SeedSigner/seedsigner/docs/Seed_QR_Card.pdf

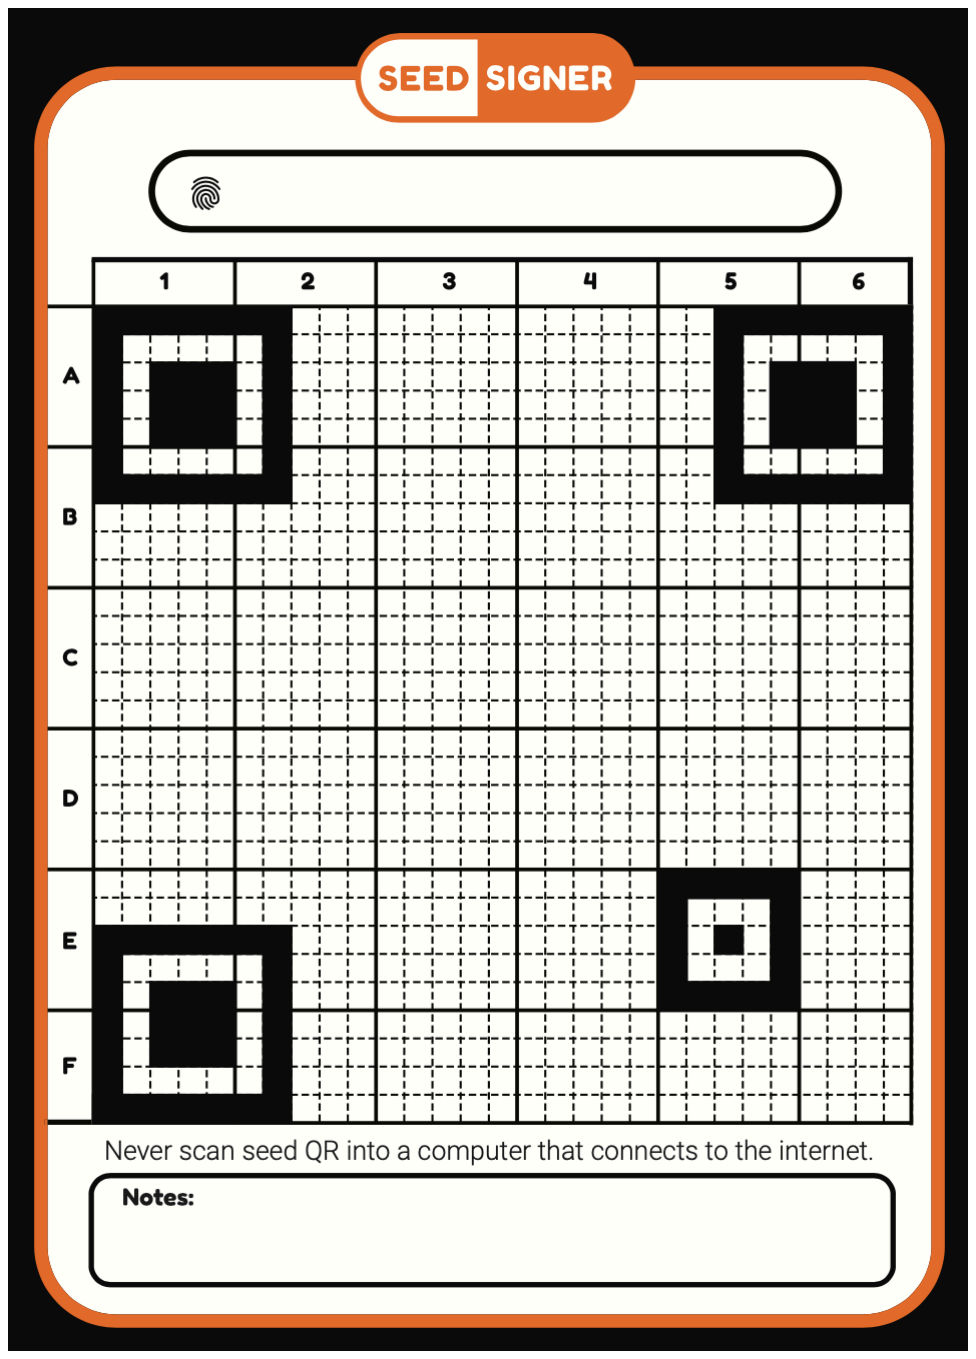
[picture p57: figure]
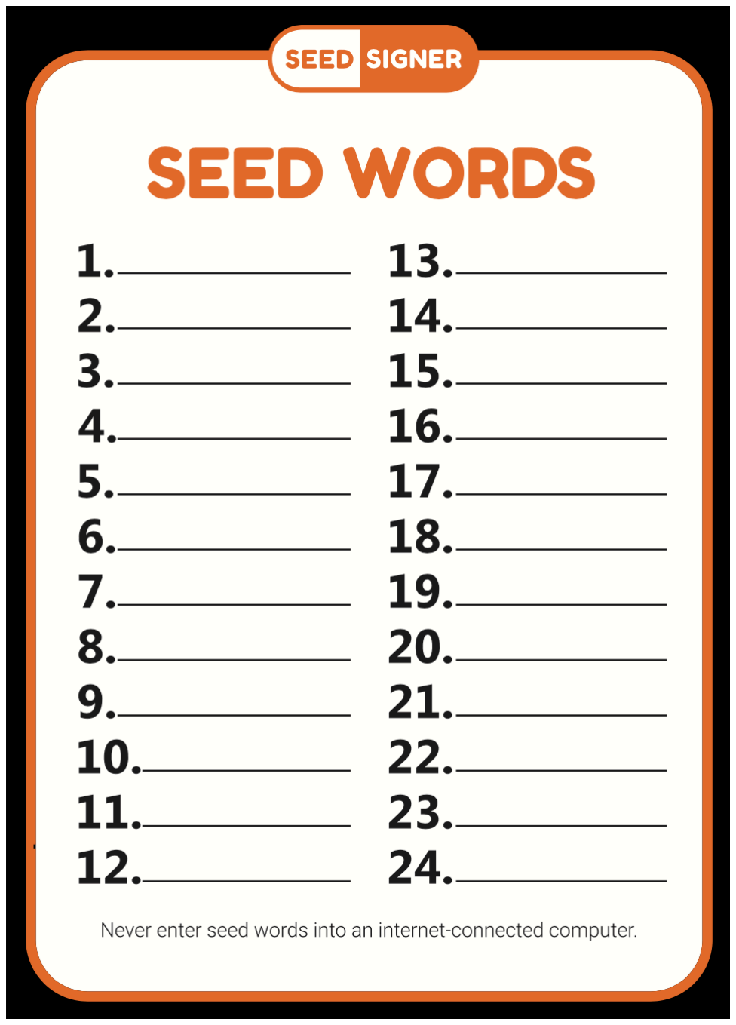
[picture p58: figure]
