SeedSigner/seedsigner/docs/img/dice_pic1.png

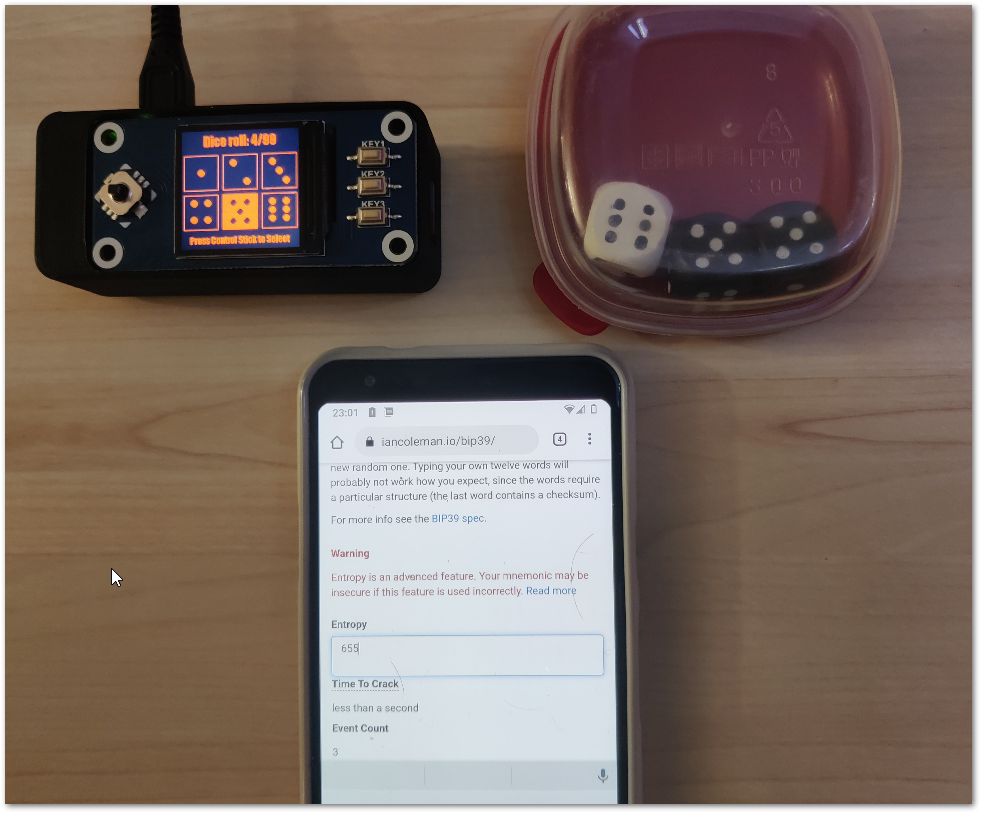
docs/img/dice_pic1.png
