SeedSigner/seedsigner/docs/img/dice_pic2.png

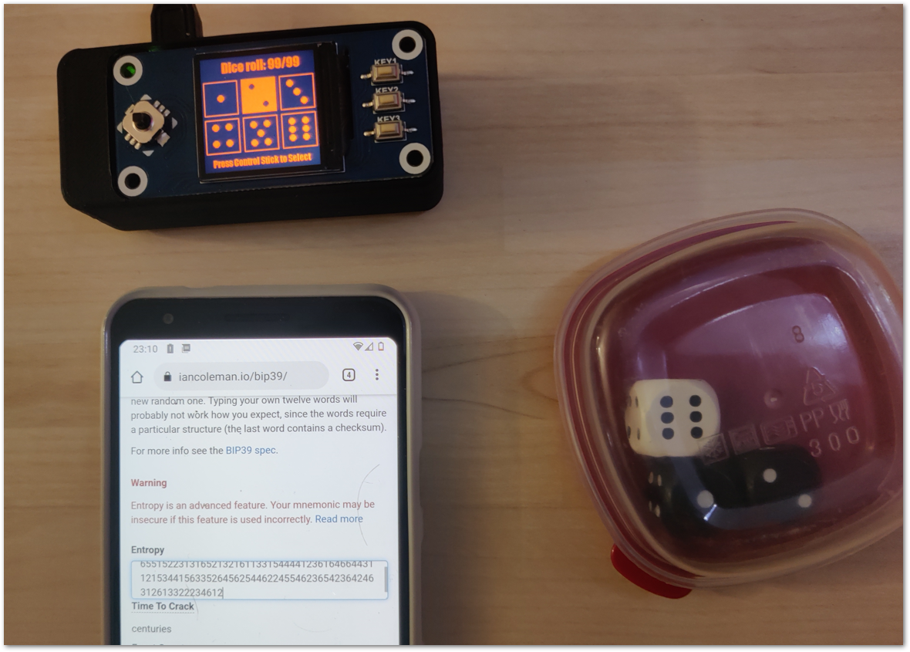
docs/img/dice_pic2.png
