SeedSigner/seedsigner/docs/img/dice_pic3.png

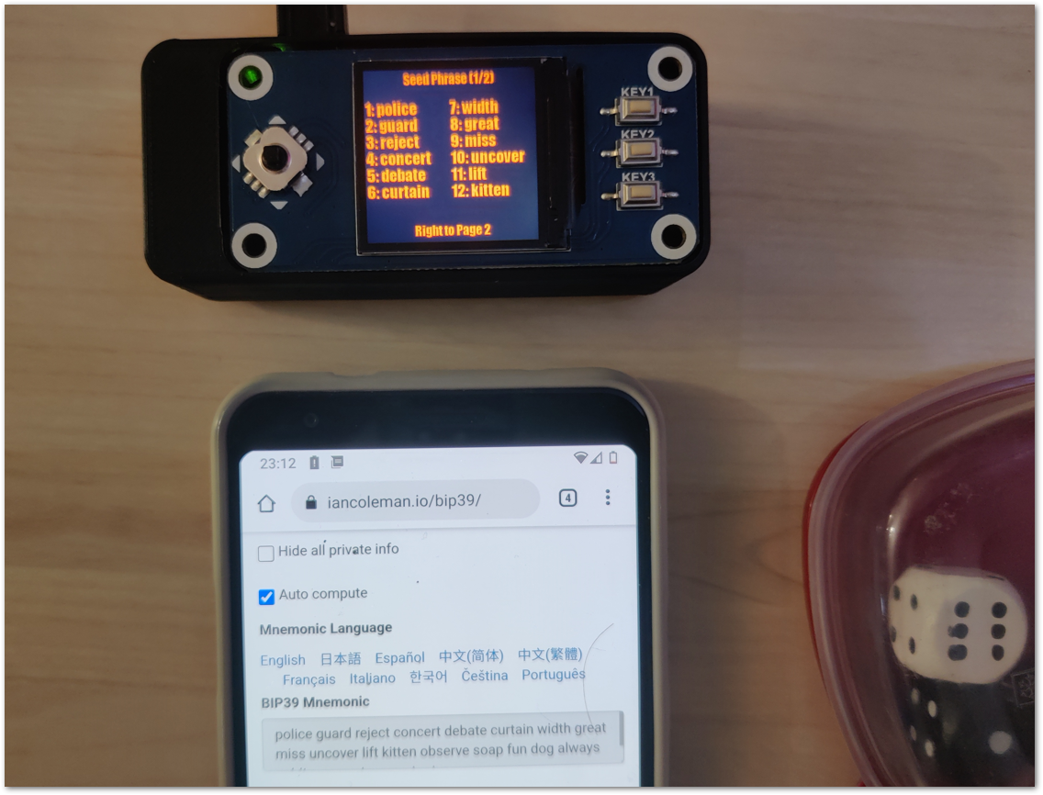
docs/img/dice_pic3.png
