SeedSigner/seedsigner/docs/img/dice_type.png

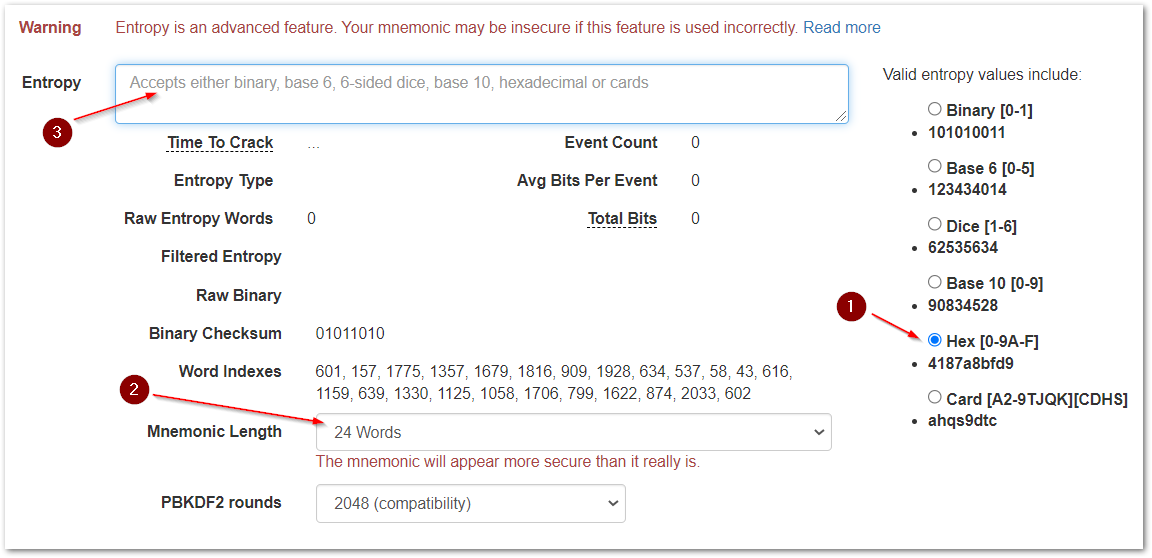
docs/img/dice_type.png
