SeedSigner/seedsigner/docs/img/Open_Pill_Star.JPG

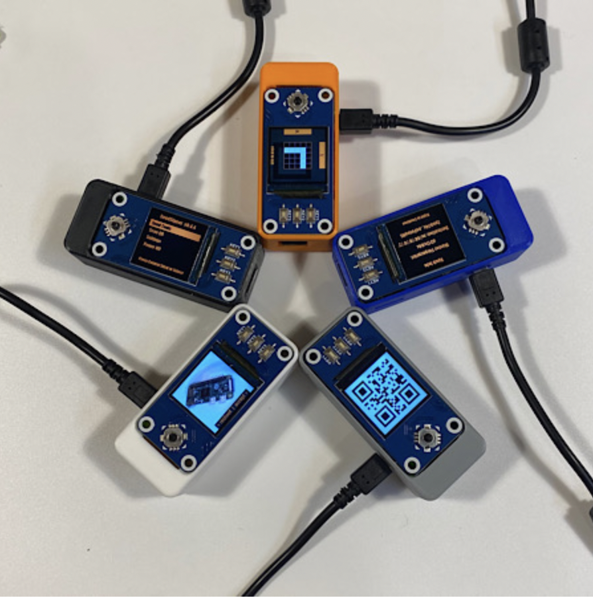
docs/img/Open_Pill_Star.JPG
