SeedSigner/seedsigner/docs/img/Orange_Pill.JPG

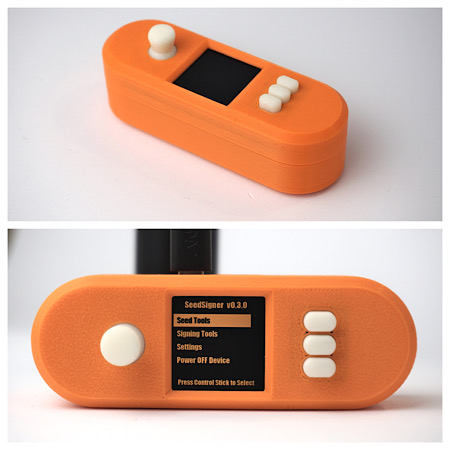
docs/img/Orange_Pill.JPG
