SeedSigner/seedsigner/docs/seed_qr/img/compact_12word.png

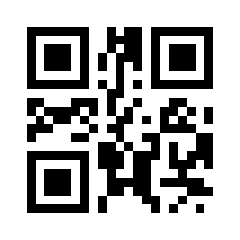
docs/seed_qr/img/compact_12word.png
