SeedSigner/seedsigner/docs/seed_qr/img/compact_24word.png

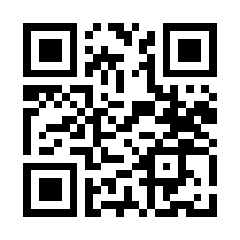
docs/seed_qr/img/compact_24word.png
