SeedSigner/seedsigner/docs/seed_qr/img/standard_24word.png

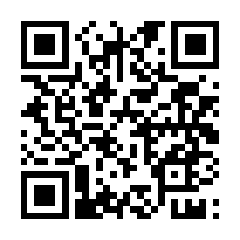
docs/seed_qr/img/standard_24word.png
