SeedSigner/seedsigner/enclosures/rugged_pill/Multimaterial/RuggedPill_Top_MMU.3mf

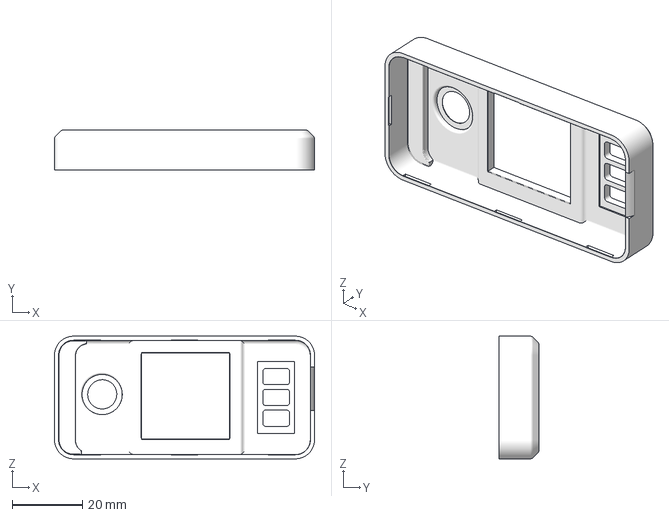
[picture p84: CAD file, 2023-07-31]
enclosures/rugged_pill/Multimaterial/RuggedPill_Top_MMU.3mf
73.8 x 11.3 x 34.8 mm
Circumference (4)
Top_MMU
