SeedSigner/seedsigner/enclosures/rugged_pill/RuggedPill_Thumbstick.stl

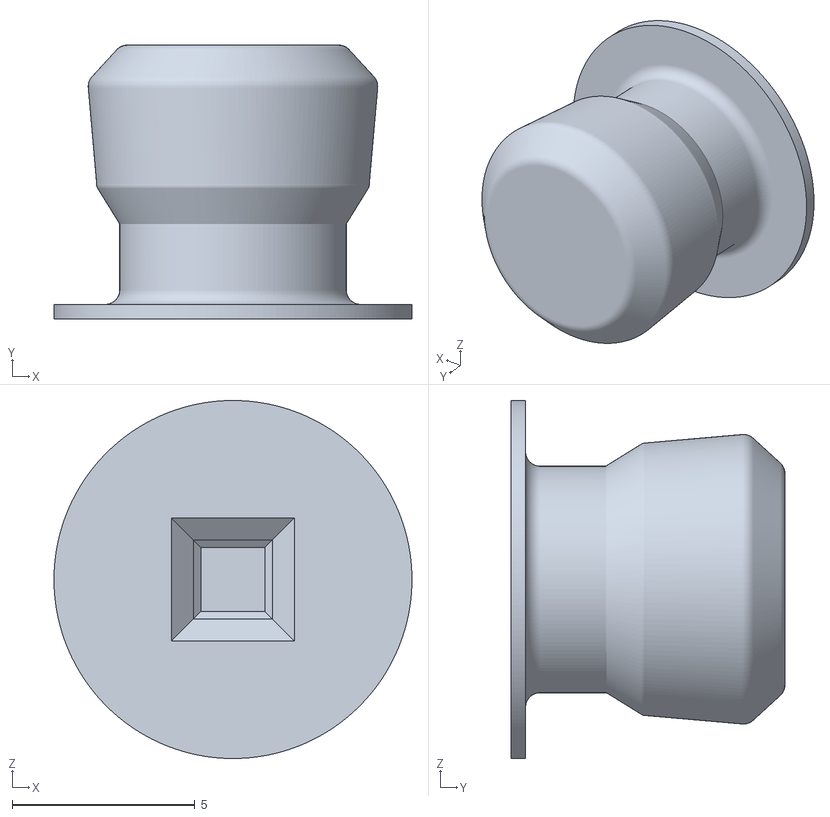
[picture p85: CAD file, 2023-07-31]
enclosures/rugged_pill/RuggedPill_Thumbstick.stl
9.80 x 7.50 x 9.80
