SeedSigner/seedsigner/enclosures/simple_pill/protective_case/sp_protective_case_upper.stl

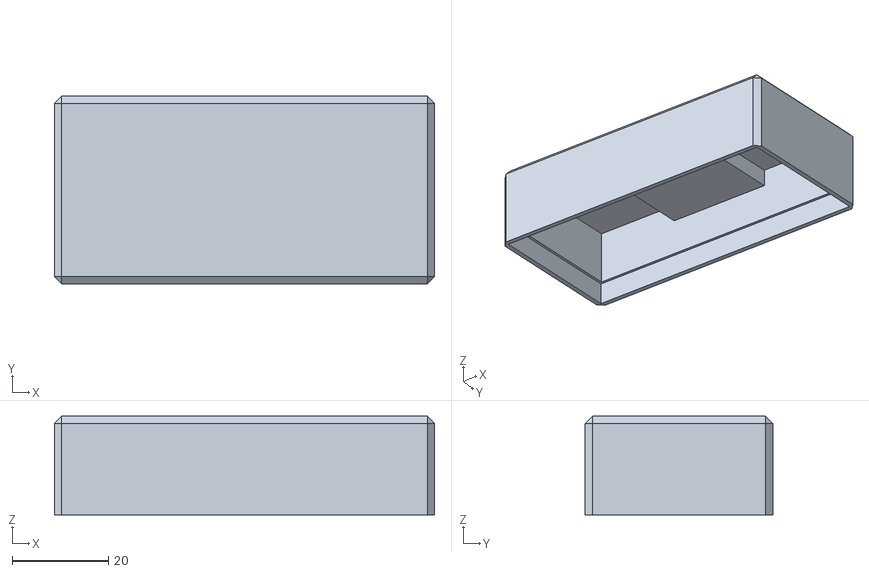
[picture p86: CAD file, 2022-12-02]
enclosures/simple_pill/protective_case/sp_protective_case_upper.stl
79.0 x 39.0 x 20.5
