SeedSigner/seedsigner/enclosures/simple_pill/sp_upper.stl

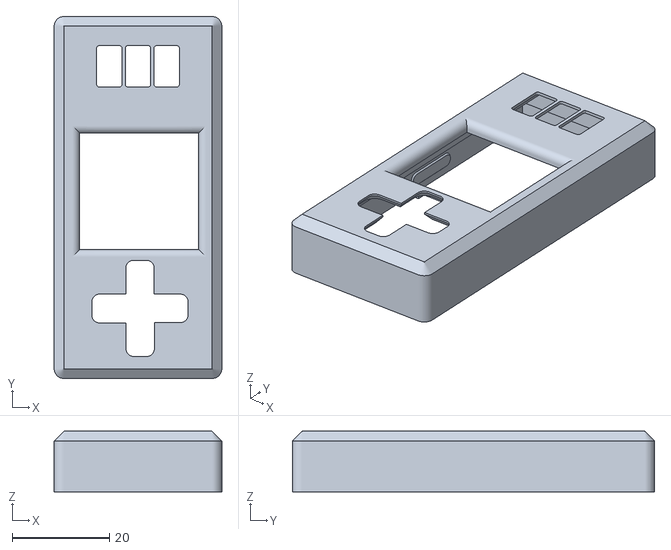
[picture p87: CAD file, 2022-05-04]
enclosures/simple_pill/sp_upper.stl
34.5 x 74.5 x 12.5
