SeedSigner/seedsigner/enclosures/open_pill_mini_w_coverplate/Thumbstick_TPU.stl

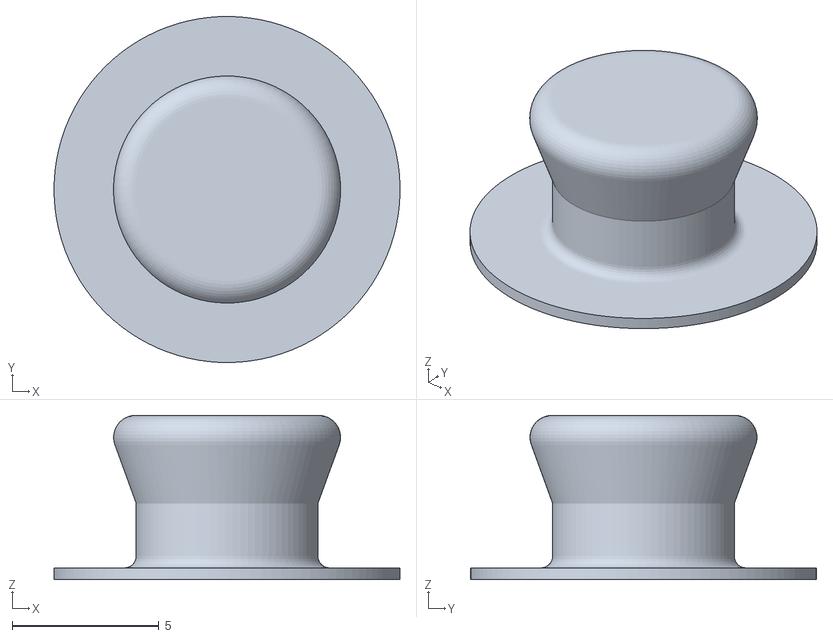
[picture p88: CAD file, 2023-02-14]
enclosures/open_pill_mini_w_coverplate/Thumbstick_TPU.stl
11.8 x 11.8 x 5.60
