SeedSigner/seedsigner/enclosures/orange_pill/print_files/button.stl

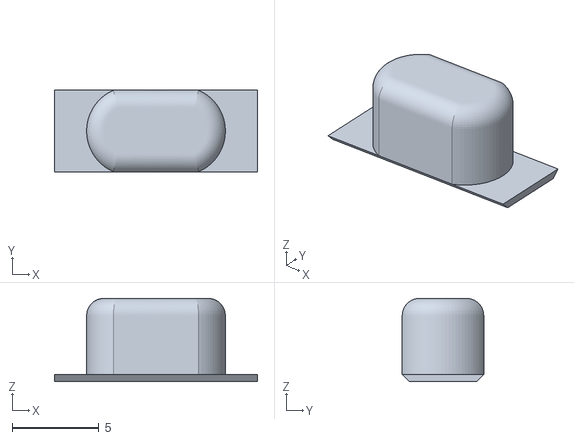
[picture p89: CAD file, 2021-04-17]
enclosures/orange_pill/print_files/button.stl
11.7 x 4.70 x 4.80
