SeedSigner/seedsigner/enclosures/pushcase/3mf/Top - Push Case - SeedSigner.3mf

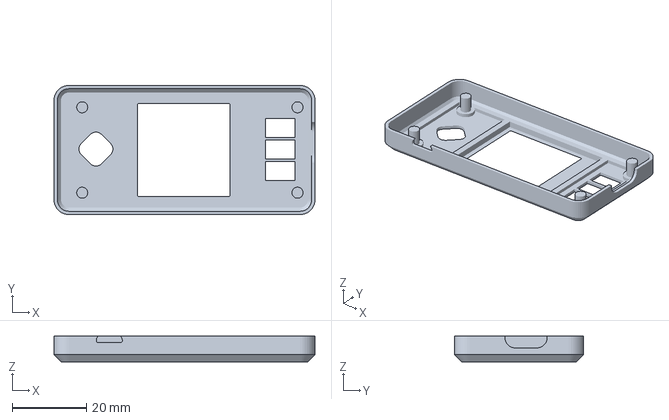
[picture p90: CAD file, 2024-07-11]
enclosures/pushcase/3mf/Top - Push Case - SeedSigner.3mf
70.3 x 34.8 x 7.00 mm
