SeedSigner/seedsigner/enclosures/rugged_pill/RuggedPill_Top.stl

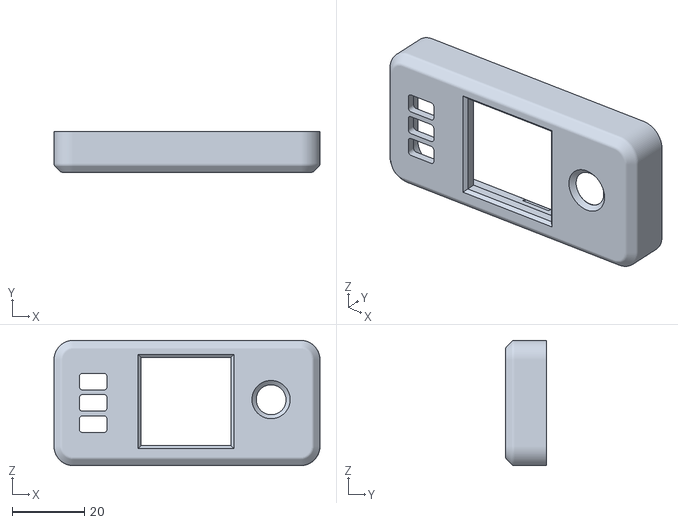
[picture p91: CAD file, 2023-07-31]
enclosures/rugged_pill/RuggedPill_Top.stl
73.8 x 11.3 x 34.8
