SeedSigner/seedsigner/enclosures/simple_pill/sp_button.stl

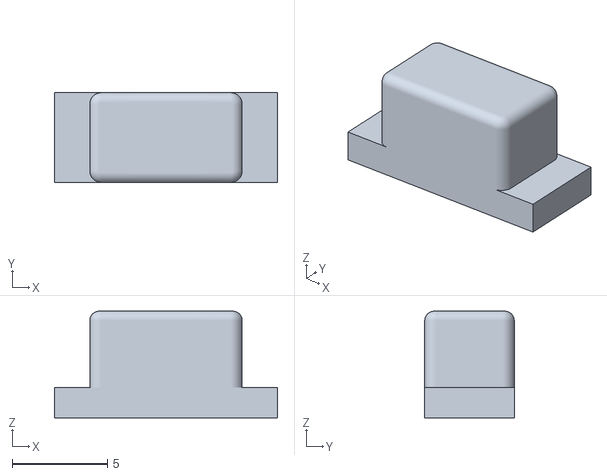
[picture p92: CAD file, 2022-05-04]
enclosures/simple_pill/sp_button.stl
11.7 x 4.70 x 5.60
