SeedSigner/seedsigner/enclosures/open_pill_mini_w_coverplate/Thumbstick_PLA.stl

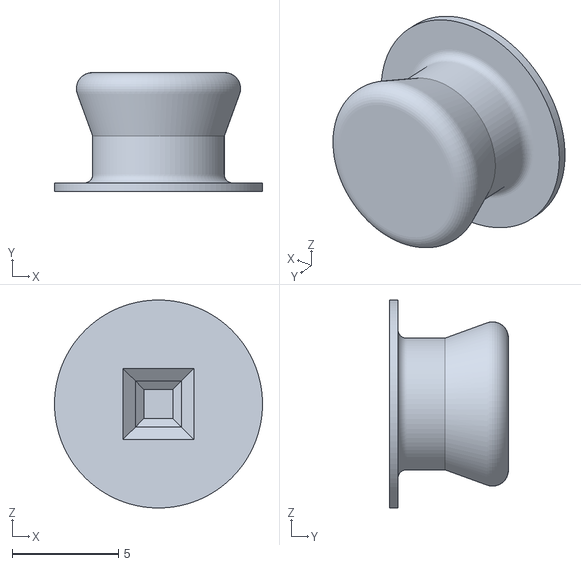
[picture p93: CAD file, 2023-02-14]
enclosures/open_pill_mini_w_coverplate/Thumbstick_PLA.stl
9.80 x 5.60 x 9.79
