SeedSigner/seedsigner/enclosures/orange_pill/print_files/OP_Upper.stl

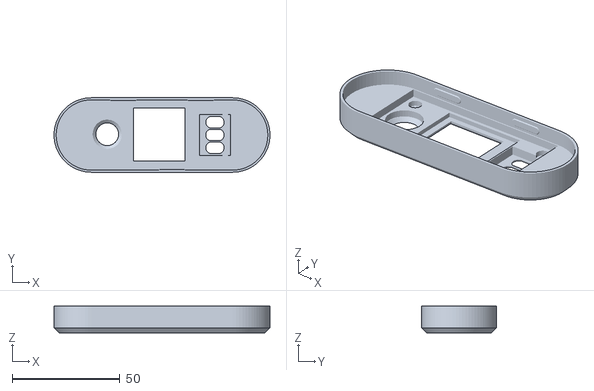
[picture p94: CAD file, 2021-04-17]
enclosures/orange_pill/print_files/OP_Upper.stl
100.0 x 34.5 x 12.5
