SeedSigner/seedsigner/enclosures/pushcase/3mf/Soldering Support - Push Case - SeedSigner.3mf

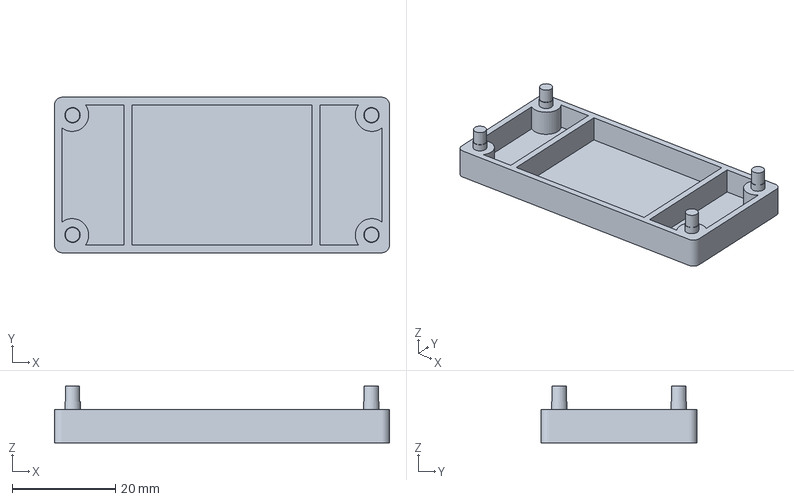
[picture p95: CAD file, 2024-07-11]
enclosures/pushcase/3mf/Soldering Support - Push Case - SeedSigner.3mf
65.0 x 30.2 x 11.0 mm
