SeedSigner/seedsigner/enclosures/rugged_pill/RuggedPill_Trackball.stl

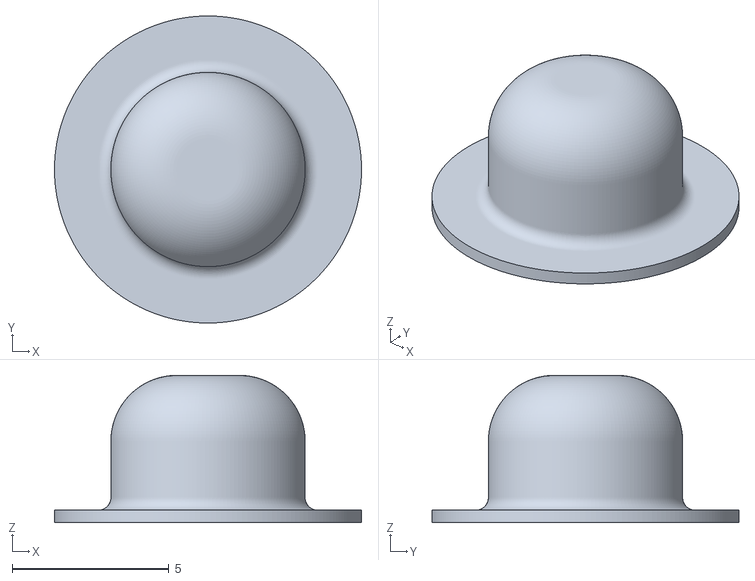
[picture p96: CAD file, 2023-07-31]
enclosures/rugged_pill/RuggedPill_Trackball.stl
9.80 x 9.80 x 4.70
