SeedSigner/seedsigner/enclosures/simple_pill/sp_dpad.stl

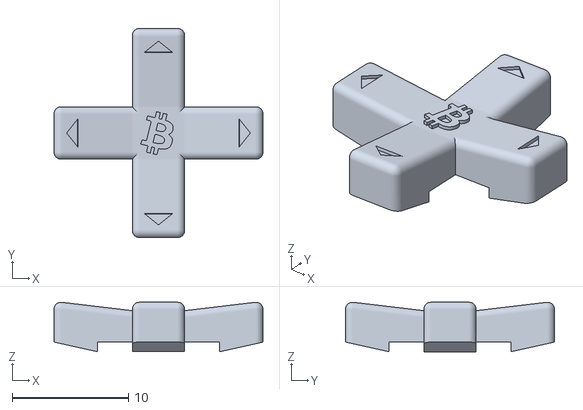
[picture p97: CAD file, 2022-05-04]
enclosures/simple_pill/sp_dpad.stl
18.0 x 18.0 x 4.26
