SeedSigner/seedsigner/enclosures/open_pill_mini_w_coverplate/Buttons.stl

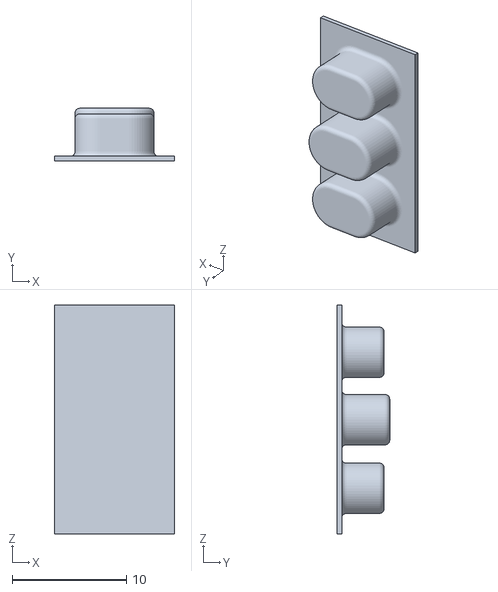
[picture p98: CAD file, 2023-02-14]
enclosures/open_pill_mini_w_coverplate/Buttons.stl
10.5 x 4.60 x 20.0
