SeedSigner/seedsigner/enclosures/pushcase/3mf/Middle - Push Case - SeedSigner.3mf

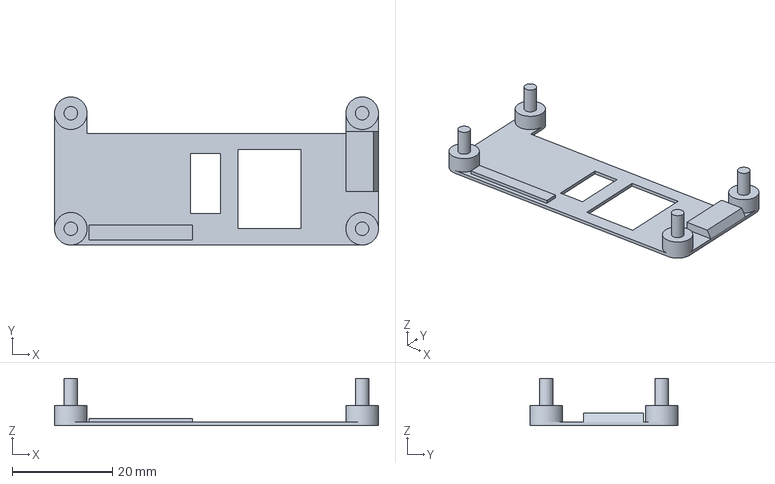
[picture p99: CAD file, 2024-07-11]
enclosures/pushcase/3mf/Middle - Push Case - SeedSigner.3mf
64.5 x 29.5 x 9.40 mm
