SeedSigner/seedsigner/enclosures/rugged_pill/RuggedPill_Buttons.stl

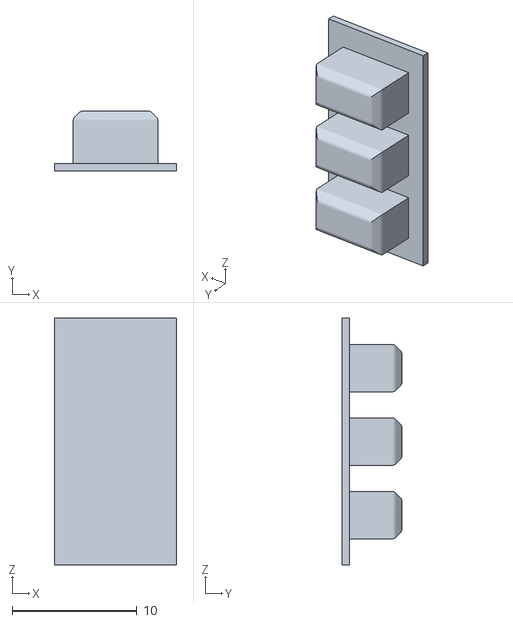
[picture p100: CAD file, 2023-07-31]
enclosures/rugged_pill/RuggedPill_Buttons.stl
9.80 x 4.80 x 19.8
