SeedSigner/seedsigner/docs/seed_qr/printable_templates/grid_wfingerprint_21x21_4-up.pdf

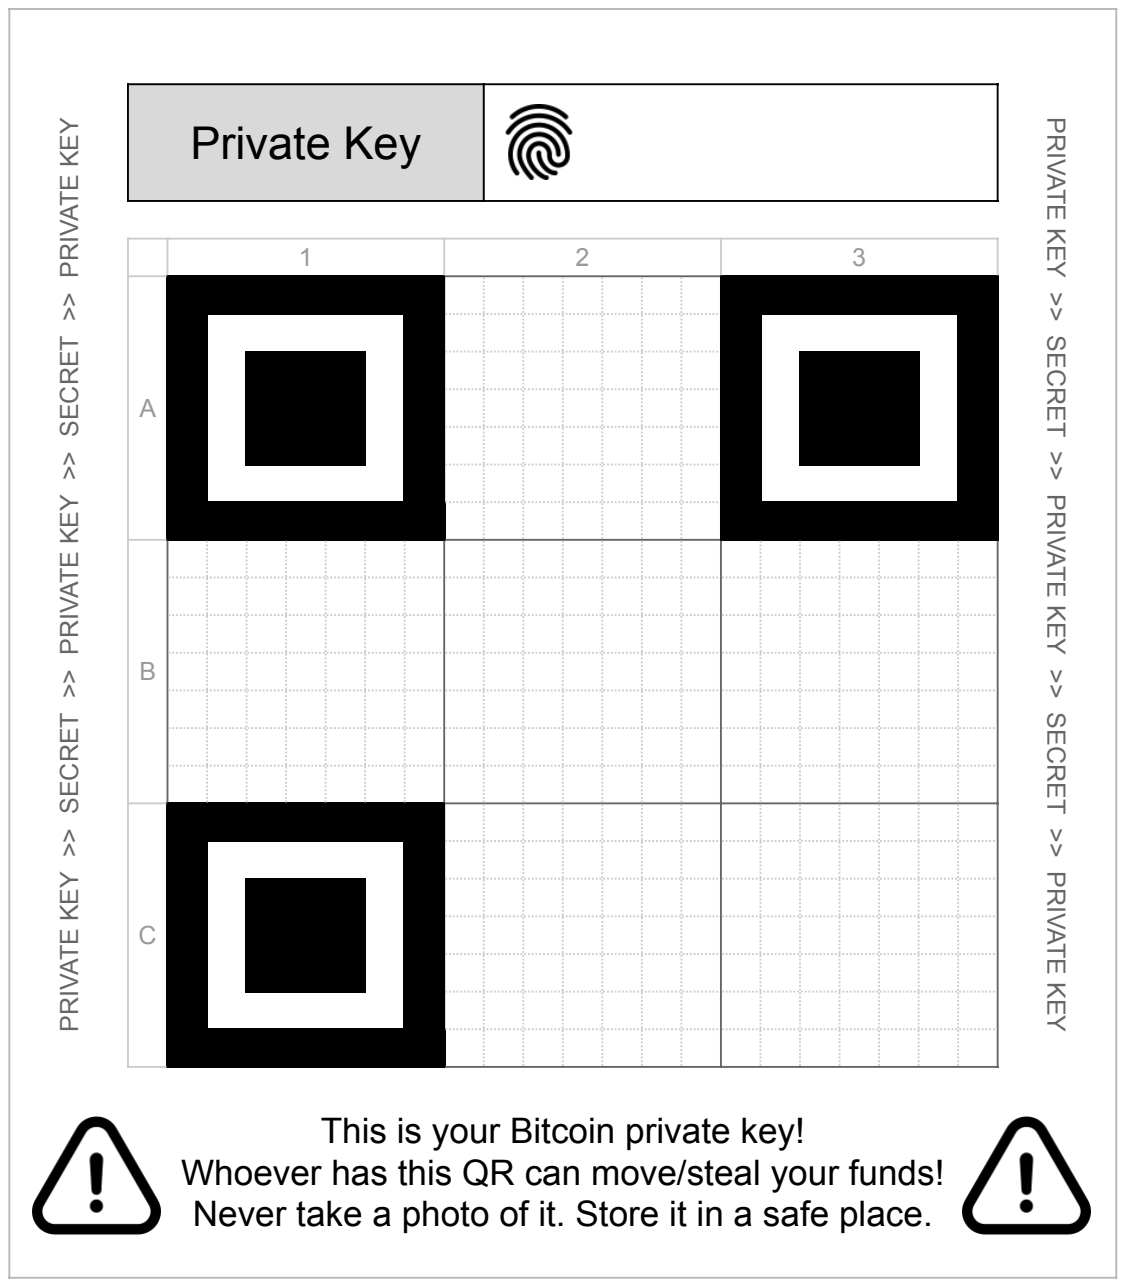
[picture p109: figure]
Private Key; This is your Bitcoin private key!

PRIVATE KEY >> SECRET >> PRIVATE KEY >> SECRET >> PRIVATE KEY PRIVATE KEY >> SECRET >> PRIVATE KEY >> SECRET >> PRIVATE KEY

Whoever has this QR can move/steal your funds! Never take a photo of it. Store it in a safe place.

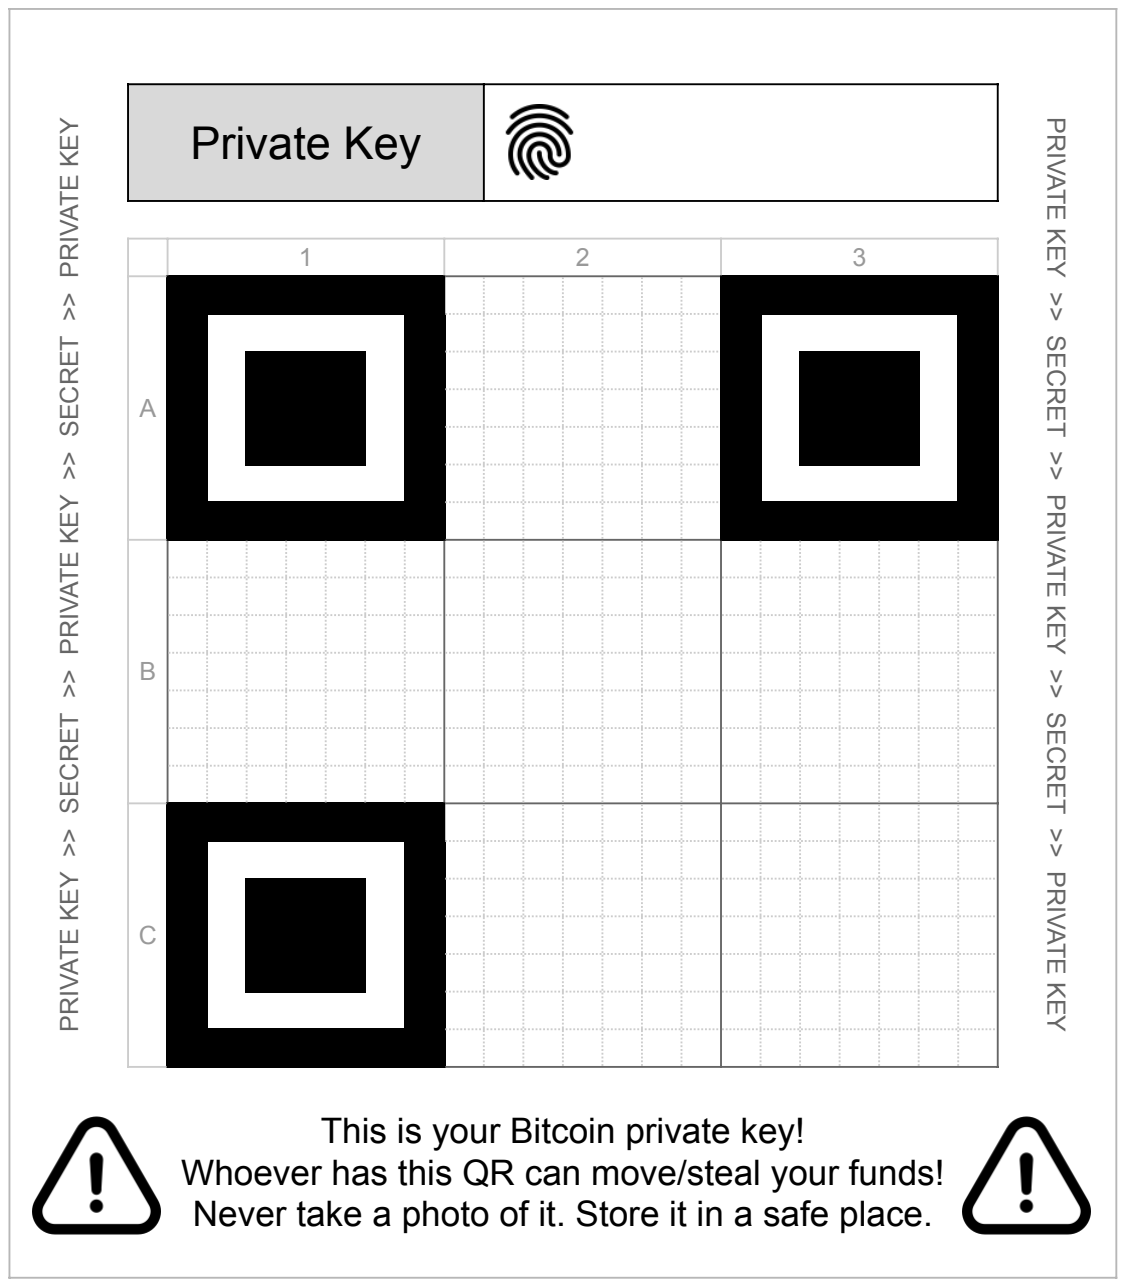
[picture p110: figure]
Private Key; This is your Bitcoin private key!

PRIVATE KEY >> SECRET >> PRIVATE KEY >> SECRET >> PRIVATE KEY PRIVATE KEY >> SECRET >> PRIVATE KEY >> SECRET >> PRIVATE KEY

Whoever has this QR can move/steal your funds! Never take a photo of it. Store it in a safe place.

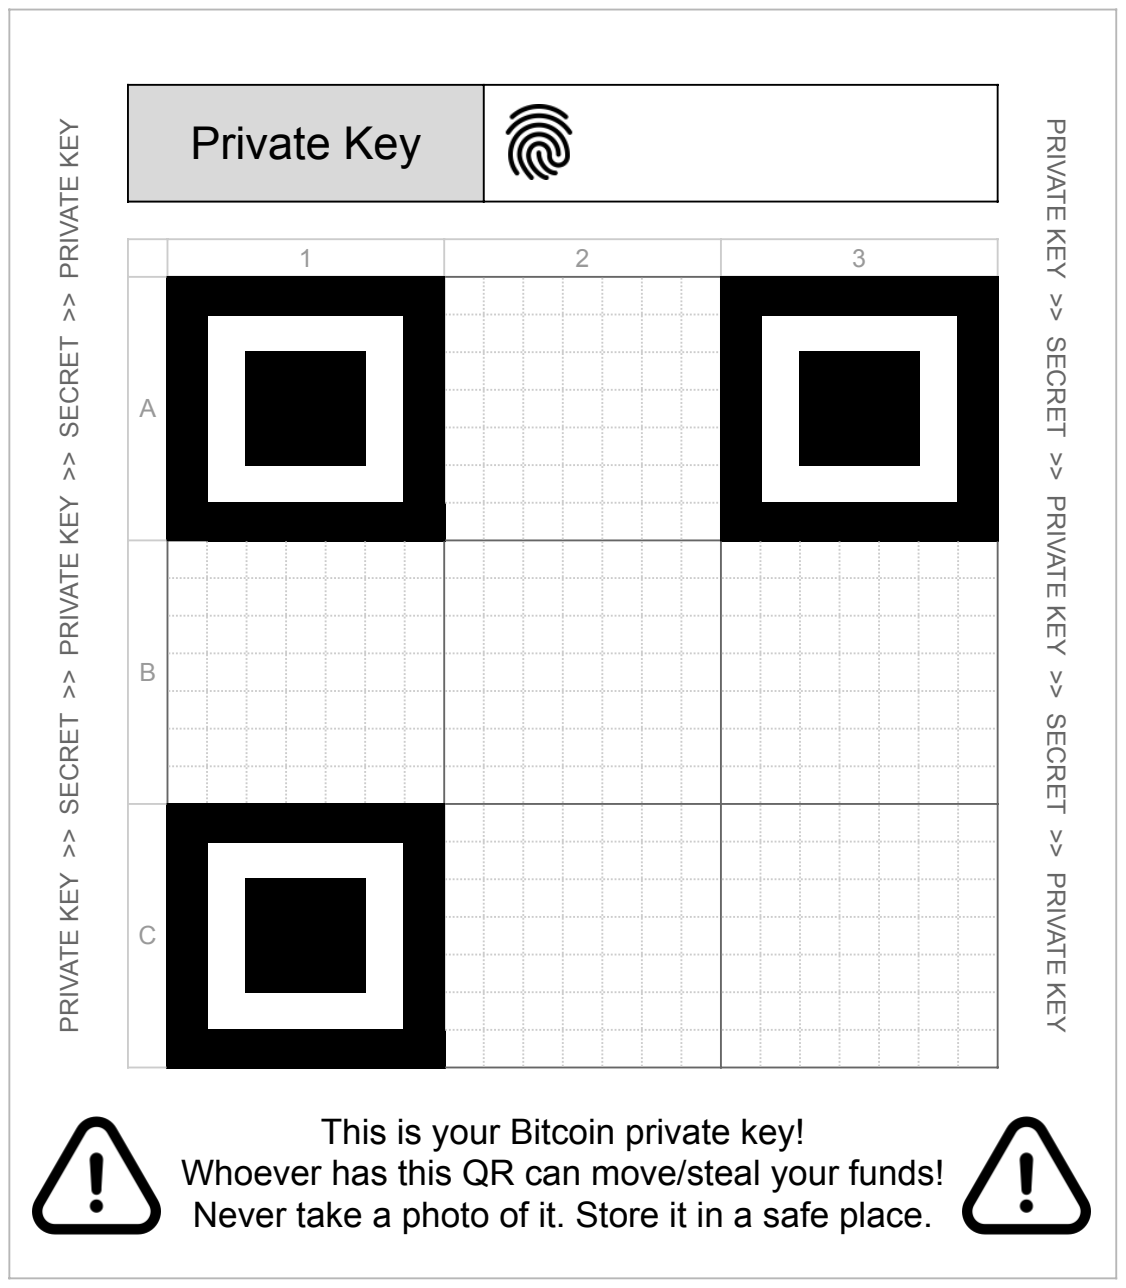
[picture p111: figure]
Private Key; This is your Bitcoin private key!

PRIVATE KEY >> SECRET >> PRIVATE KEY >> SECRET >> PRIVATE KEY PRIVATE KEY >> SECRET >> PRIVATE KEY >> SECRET >> PRIVATE KEY

Whoever has this QR can move/steal your funds! Never take a photo of it. Store it in a safe place.

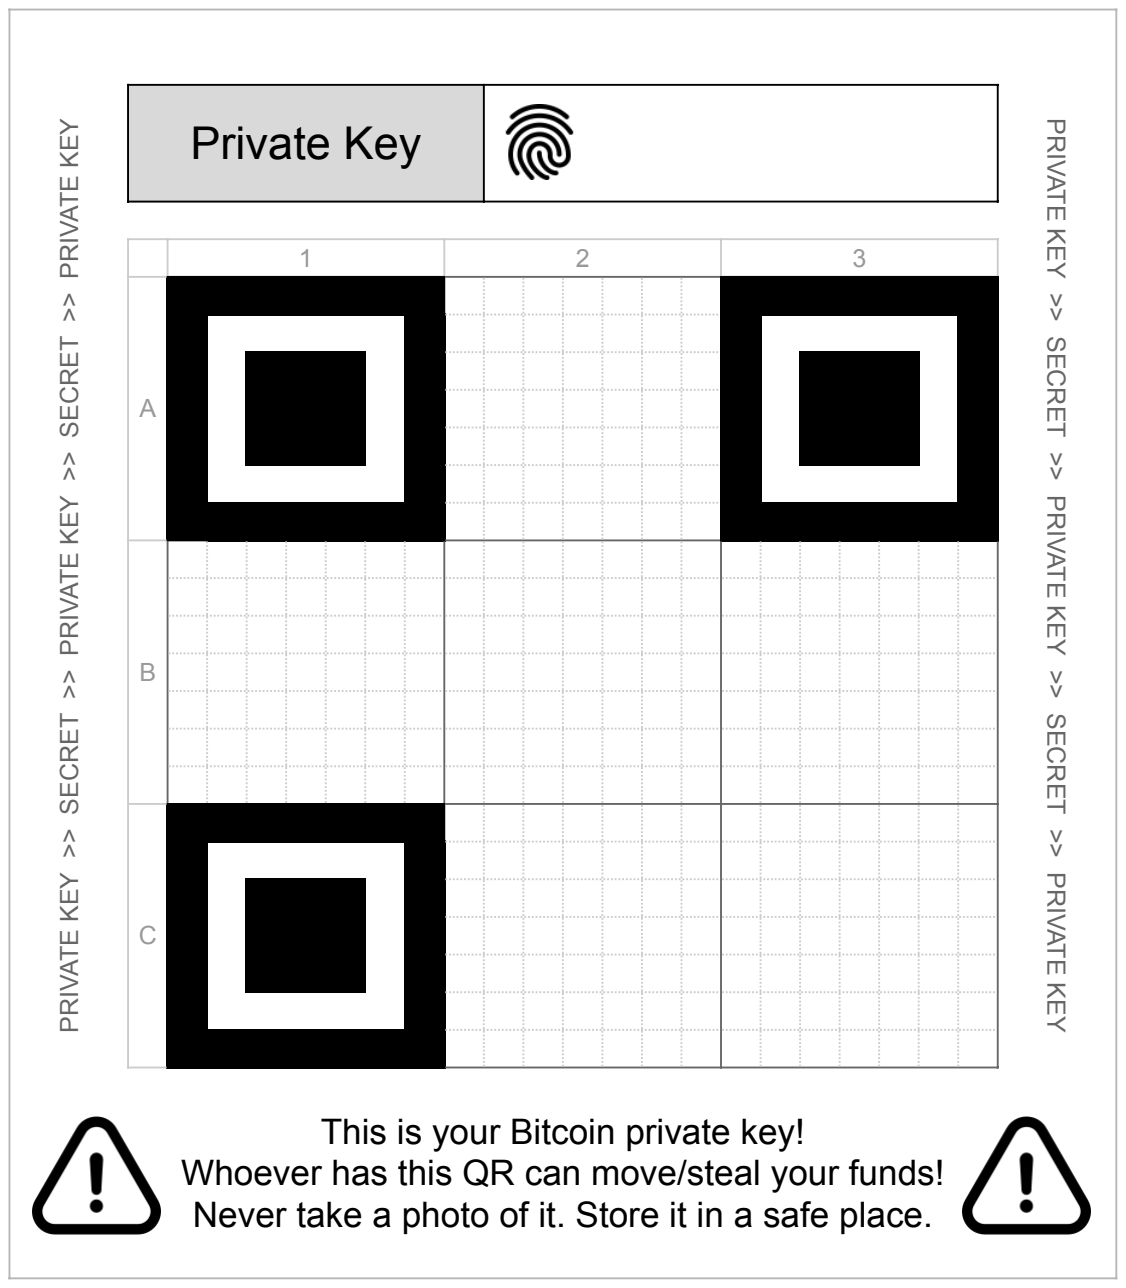
[picture p112: figure]
Private Key; This is your Bitcoin private key!

PRIVATE KEY >> SECRET >> PRIVATE KEY >> SECRET >> PRIVATE KEY PRIVATE KEY >> SECRET >> PRIVATE KEY >> SECRET >> PRIVATE KEY

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
