SeedSigner/seedsigner/docs/seed_qr/printable_templates/mnemonic_12words_wfingerprint.pdf

PRIVATE KEY >> SECRET >> PRIVATE KEY >> SECRET >> PRIVATE KEY >> SECRET

PRIVATE KEY >> SECRET >> PRIVATE KEY >> SECRET >> PRIVATE KEY >> SECRET

Private Key

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
______________________

______________________

______________________

______________________

______________________

______________________

______________________

______________________

______________________

______________________

______________________

______________________ This is your Bitcoin private key!

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
al y

o

u

r

f

u

n

d

s! Never make a digital copy. Store it in a safe plac e.
