SeedSigner/seedsigner/docs/seed_qr/printable_templates/mnemonic_12words_wfingerprint_4up.pdf

PRIVATE KEY >> SECRET >> PRIVATE KEY >> SECRET >> PRIVATE KEY >> SECRET
PRIVATE KEY >> SECRET >> PRIVATE KEY >> SECRET >> PRIVATE KEY >> SECRET

Private Key

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
______________________

______________________

______________________

______________________

______________________

______________________

______________________

______________________

______________________

______________________

______________________

______________________ This is your Bitcoin private key!

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
PRIVATE KEY >> SECRET >> PRIVATE KEY >> SECRET >> PRIVATE KEY >> SECRET
PRIVATE KEY >> SECRET >> PRIVATE KEY >> SECRET >> PRIVATE KEY >> SECRET

Private Key

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
______________________

______________________

______________________

______________________

______________________

______________________

______________________

______________________

______________________

______________________

______________________

______________________ This is your Bitcoin private key!

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
PRIVATE KEY >> SECRET >> PRIVATE KEY >> SECRET >> PRIVATE KEY >> SECRET
PRIVATE KEY >> SECRET >> PRIVATE KEY >> SECRET >> PRIVATE KEY >> SECRET

Private Key

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
______________________

______________________

______________________

______________________

______________________

______________________

______________________

______________________

______________________

______________________

______________________

______________________ This is your Bitcoin private key!

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
PRIVATE KEY >> SECRET >> PRIVATE KEY >> SECRET >> PRIVATE KEY >> SECRET
PRIVATE KEY >> SECRET >> PRIVATE KEY >> SECRET >> PRIVATE KEY >> SECRET

Private Key

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
______________________

______________________

______________________

______________________

______________________

______________________

______________________

______________________

______________________

______________________

______________________

______________________ This is your Bitcoin private key!

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
