SeedSigner/seedsigner/docs/seed_qr/printable_templates/mnemonic_24word_wfingerprint.pdf

PRIVATE KEY >> SECRET >> PRIVATE KEY >> SECRET >> PRIVATE KEY >> SECRET

Private Key

PRIVATE KEY >> SECRET >> PRIVATE KEY >> SECRET >> PRIVATE KEY >> SECRET
1. _____________ | 13. _____________
2. _____________ | 14. _____________
3. _____________ | 15. _____________
4. _____________ | 16. _____________
5. _____________ | 17. _____________
6. _____________ | 18. _____________
7. _____________ | 19. _____________
8. _____________ | 20. _____________
9. _____________ | 21. _____________
10. _____________ | 22. _____________
11. _____________ | 23. _____________
12. _____________ | 24. _____________

This is your Bitcoin private key! Whoever has this can move/steal your funds! Never make a digital copy. Store it in a safe place.
