SeedSigner/seedsigner/docs/seed_qr/printable_templates/xpub_wfingerprint.pdf

PUBLIC KEY >> OK to scan >> PUBLIC KEY >> OK to scan >> PUBLIC KEY

PUBLIC KEY >> OK to scan >> PUBLIC KEY >> OK to scan >> PUBLIC KEY

# Public Key (aka Xpub) This is

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
blic

k

e

y. It enables view-only access to your btc b

ala

n

c

e. It is SAFE to scan this QR into wallet software. ⁽paste xpub QR code here)
