SeedSigner/seedsigner/docs/seed_qr/printable_templates/trading_card_21x21_w12words.pdf

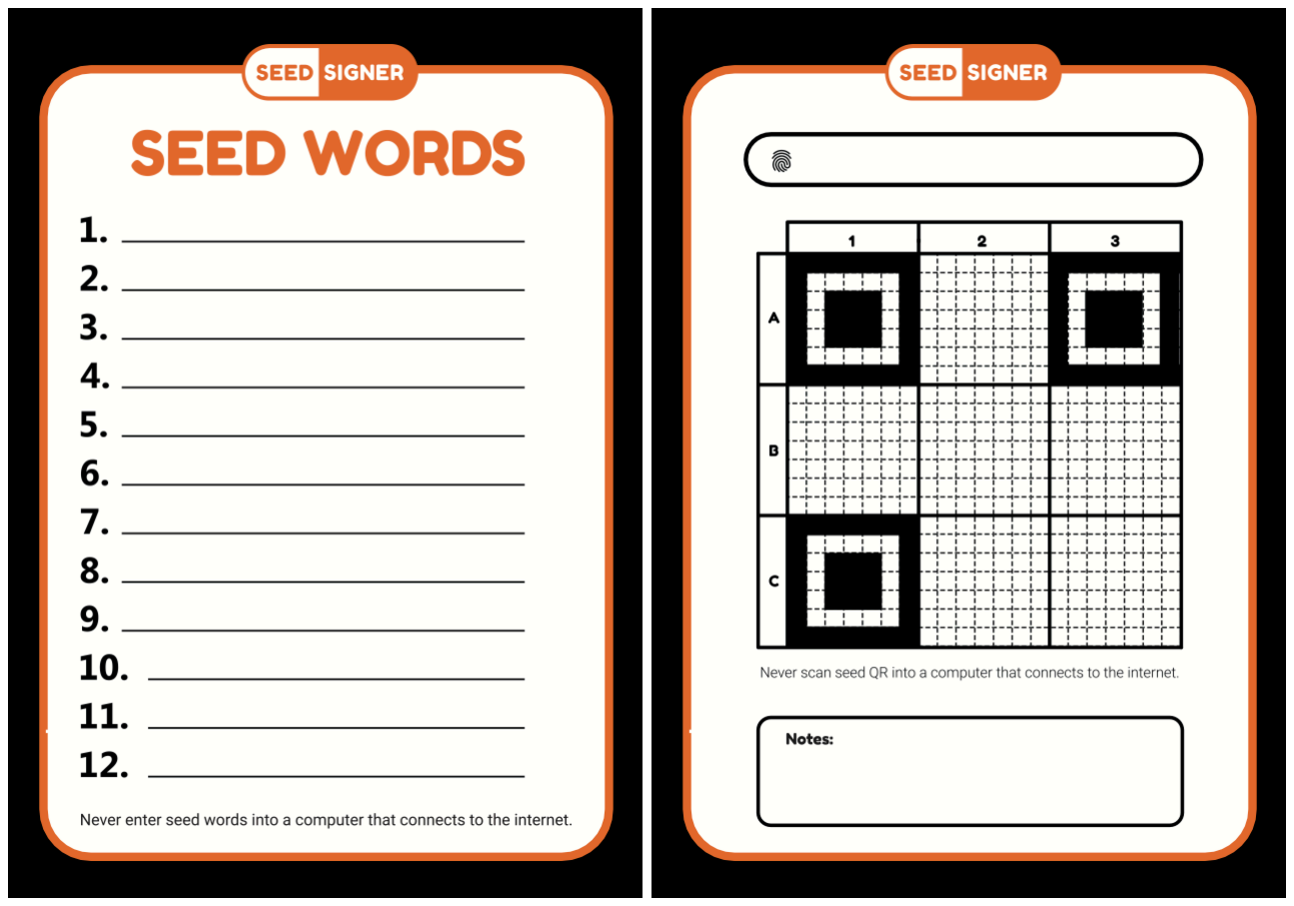
[picture p113: figure]
