SeedSigner/seedsigner/docs/seed_qr/printable_templates/trading_card_25x25_w24words.pdf

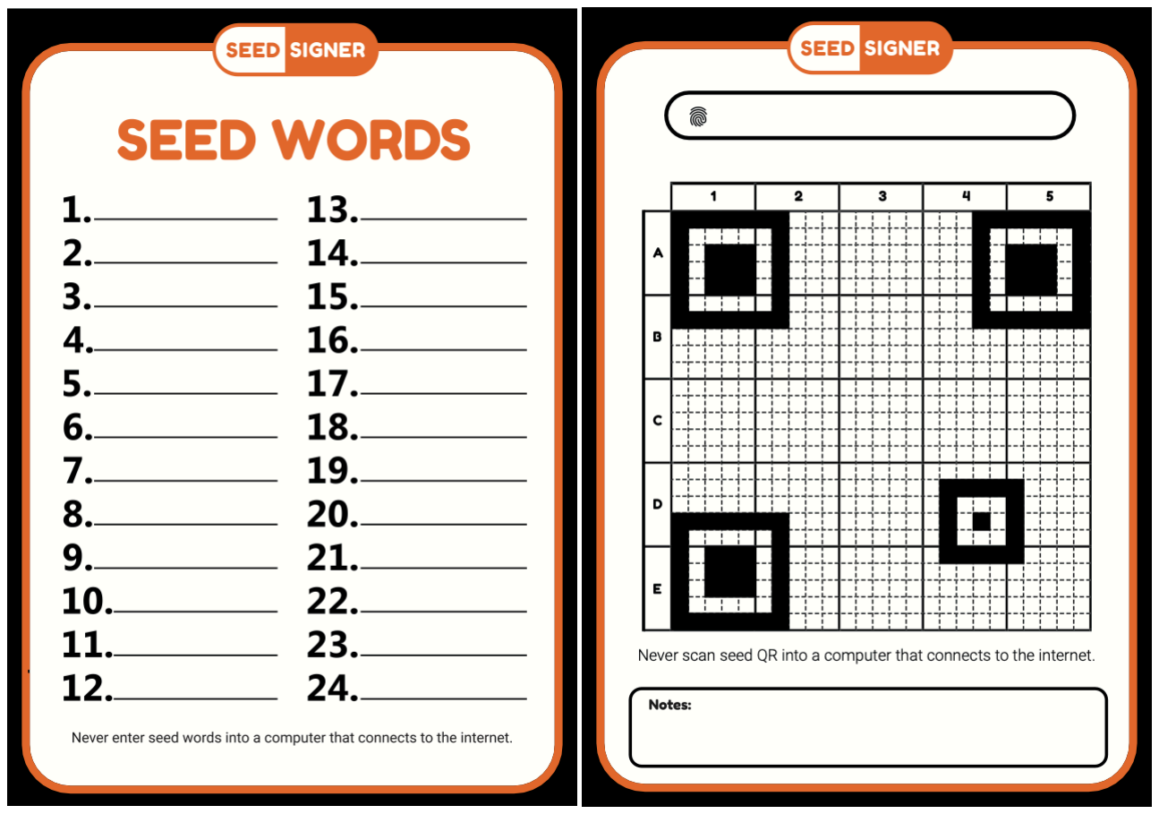
[picture p114: figure]
