SeedSigner/seedsigner/docs/seed_qr/printable_templates/trading_card_29x29_w24words.pdf

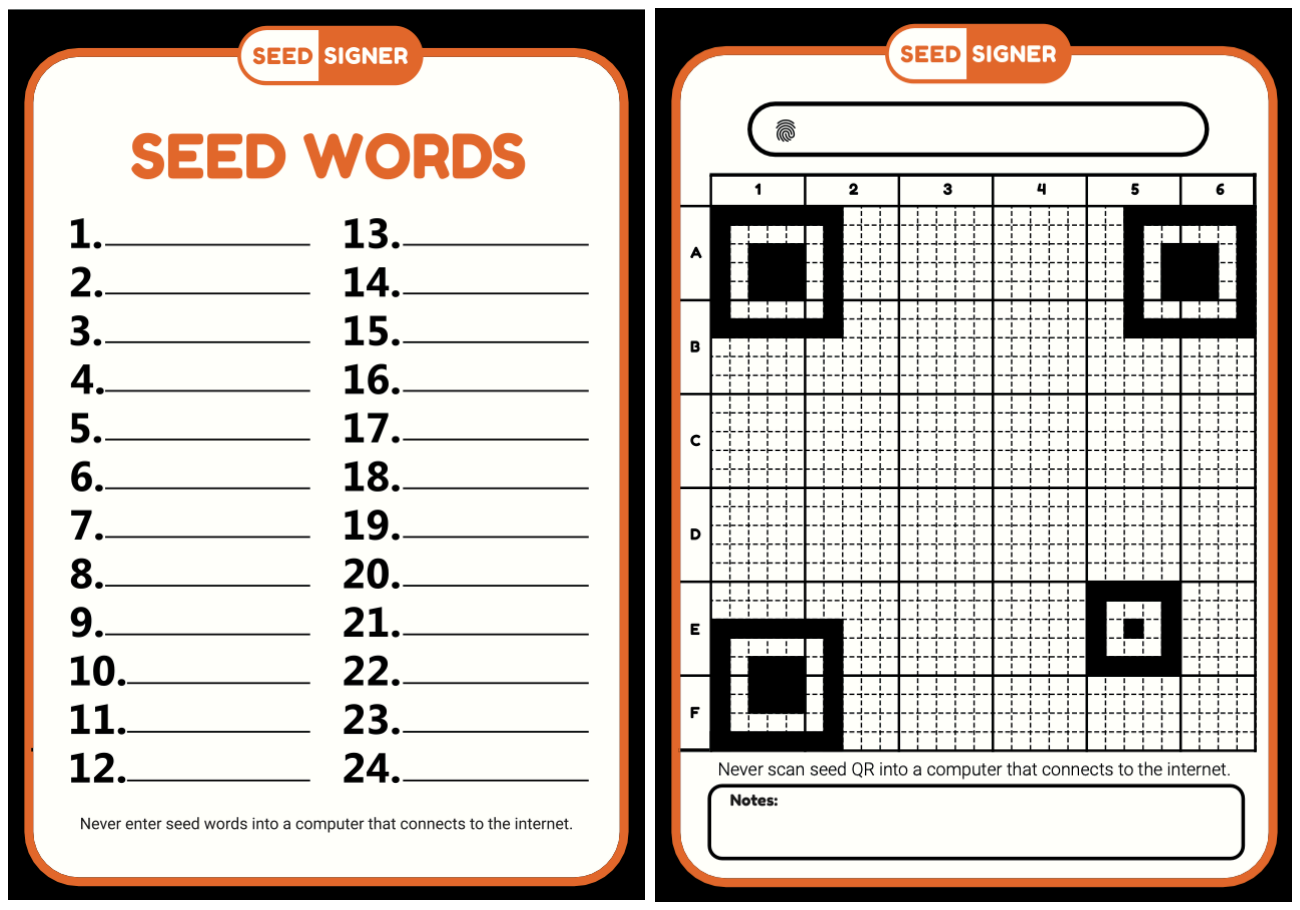
[picture p115: figure]
